Ryan-Jing/Mood-Lamp/Firmware/include/config.h

/**************************************************************************************************/
/**
 * @file config.h
 * @author  ()
 * @brief   Project configuration header.
 *
 * @version 0.1
 * @date 2026-07-07
 *
 * @copyright Copyright (c) 2026
 *
 */
/**************************************************************************************************/

#ifndef CONFIG_H
#define CONFIG_H

/*------------------------------------------------------------------------------------------------*/
// HEADERS                                                                                        */
/*------------------------------------------------------------------------------------------------*/



/*------------------------------------------------------------------------------------------------*/
// GLOBAL VARIABLES                                                                               */
/*------------------------------------------------------------------------------------------------*/

#define PRINT_DEBUG 1

#define API_TIMEOUT_MS 5000
#define PEER_POLL_INTERVAL_MS 10000
#define API_RETRY_LIMIT 5
#define SNTP_TIMEOUT_MS 15000
#define BLE_PROVISIONING_TIMEOUT_MS 120000UL

/*------------------------------------------------------------------------------------------------*/
// CLASS DECLARATIONS                                                                             */
/*------------------------------------------------------------------------------------------------*/



/*------------------------------------------------------------------------------------------------*/
// FUNCTION DECLARATIONS                                                                          */
/*------------------------------------------------------------------------------------------------*/



#endif // CONFIG_H
